renatobo/bonogps/software/connecting/racechrono/RC-working.png

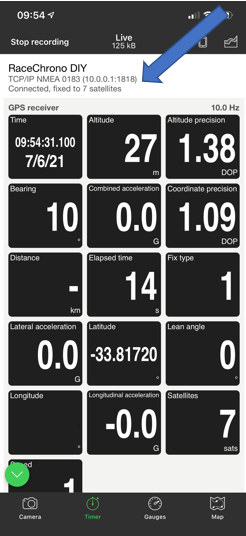
software/connecting/racechrono/RC-working.png
